RoboticsBrno/RB3201-RBControl/docs/RB3201-RBControl_LegoConnectorX1A_v1.0_board.png

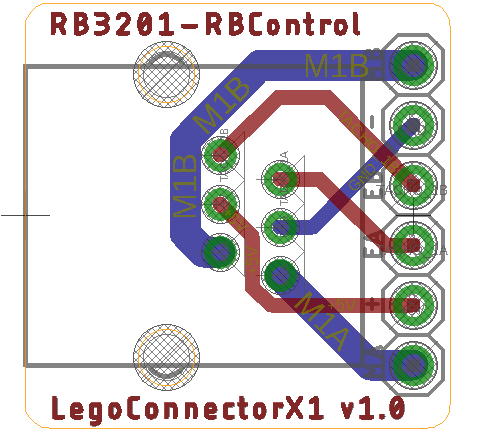
docs/RB3201-RBControl_LegoConnectorX1A_v1.0_board.png
